DEAD10C5/badge-2023-tri-poloski/images/20230513_213218.jpg

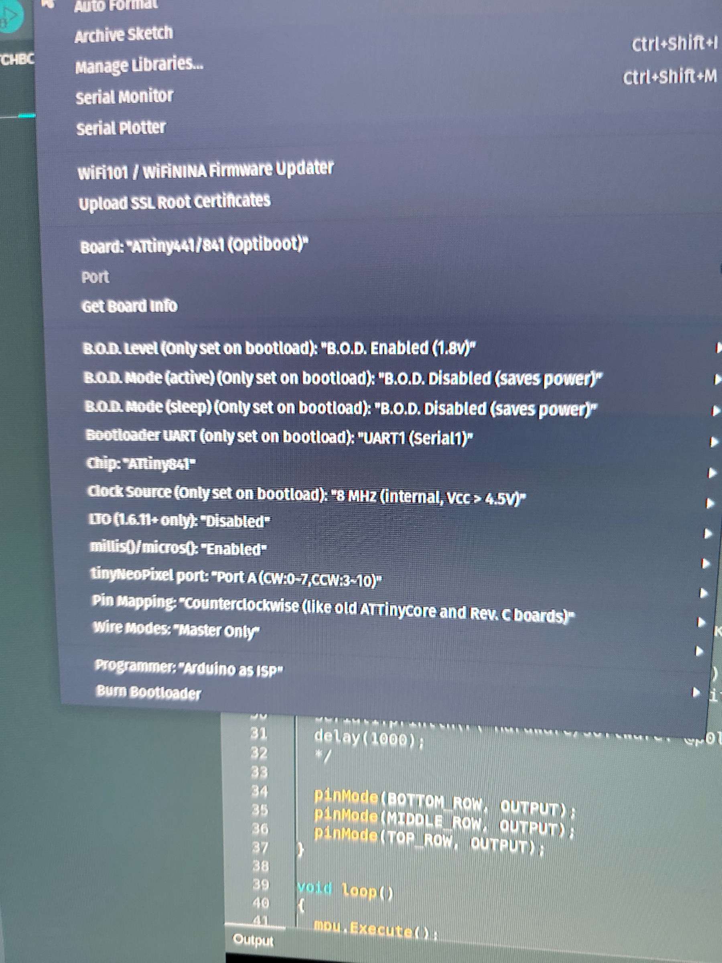
images/20230513_213218.jpg
