DEAD10C5/badge-2023-tri-poloski/images/adidas-back-3d-v2.png

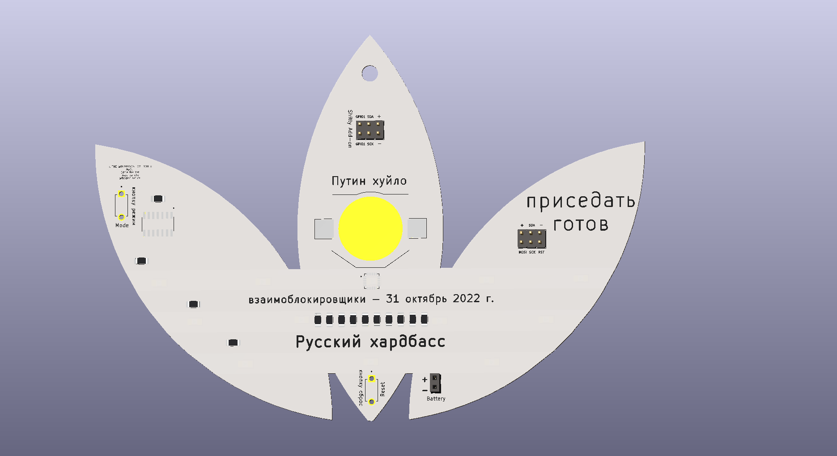
images/adidas-back-3d-v2.png
