DEAD10C5/badge-2023-tri-poloski/images/adidas-back-3d.png

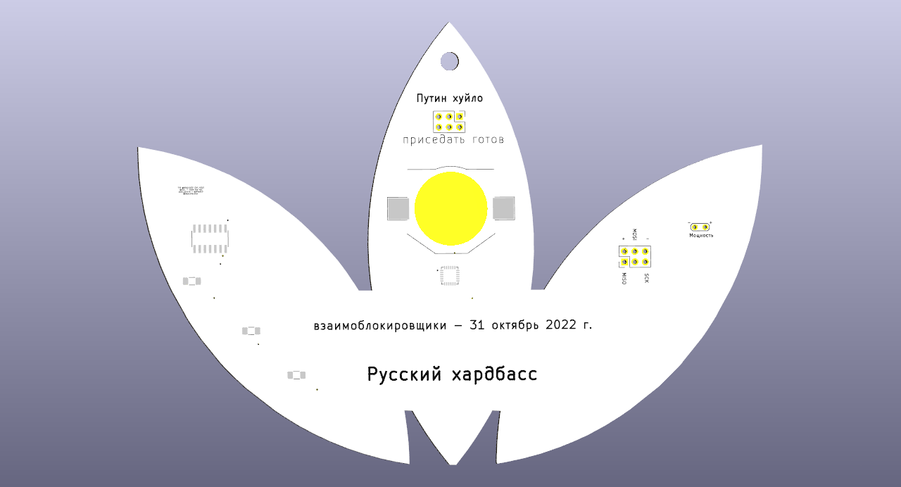
images/adidas-back-3d.png
