DEAD10C5/badge-2023-tri-poloski/images/adidas-brd2.png

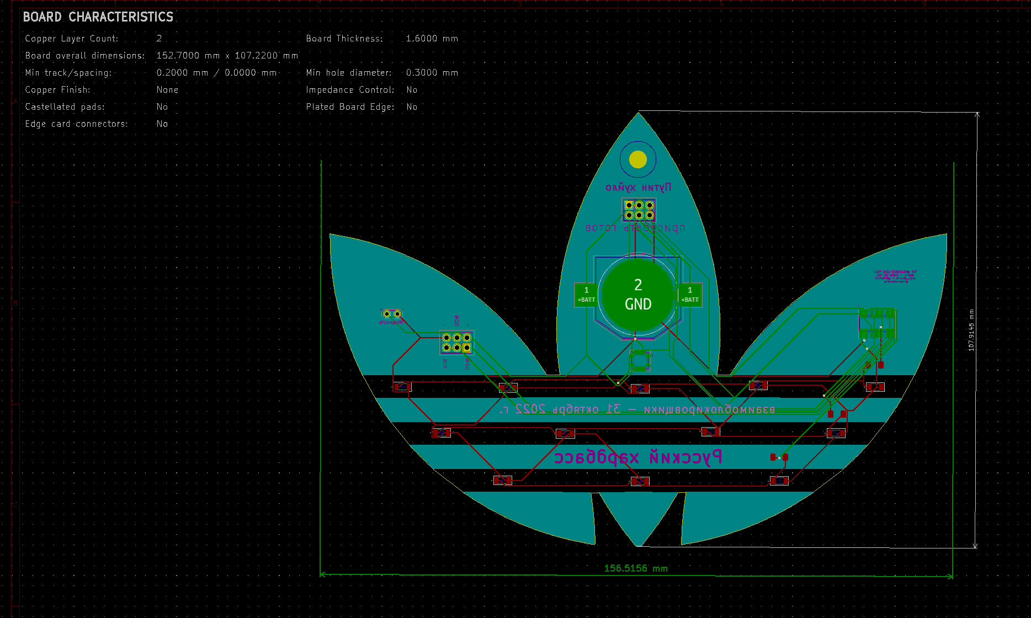
images/adidas-brd2.png
