DEAD10C5/badge-2023-tri-poloski/images/adidas-brd.png

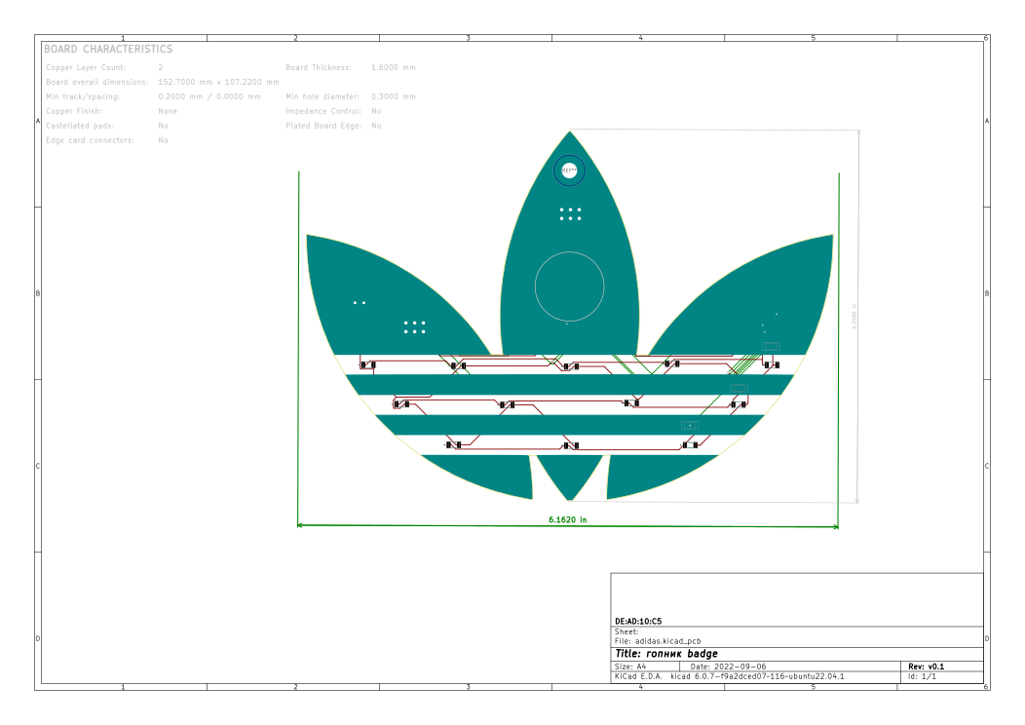
images/adidas-brd.png
