DEAD10C5/badge-2023-tri-poloski/images/adidas-front-3d.png

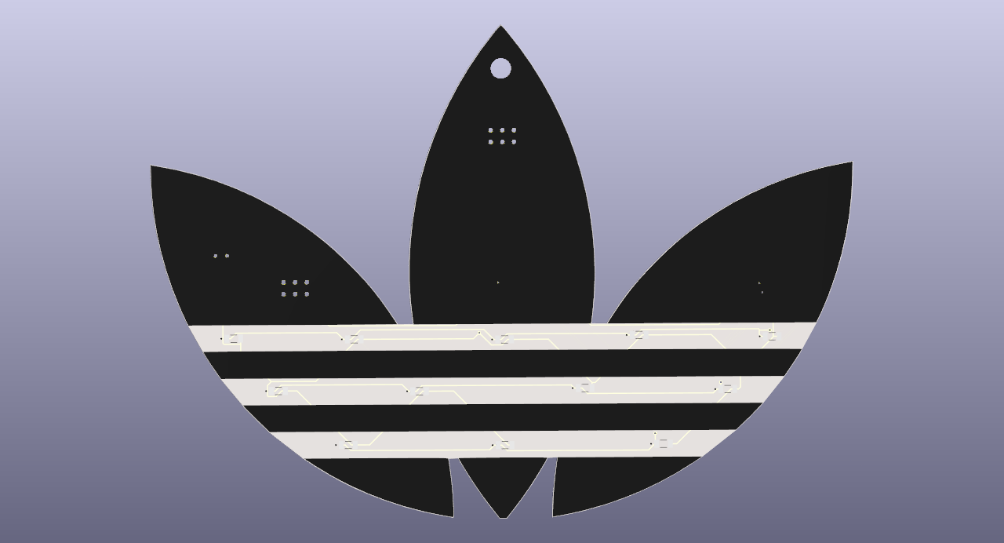
images/adidas-front-3d.png
