DEAD10C5/badge-2023-tri-poloski/images/almost_final2.png

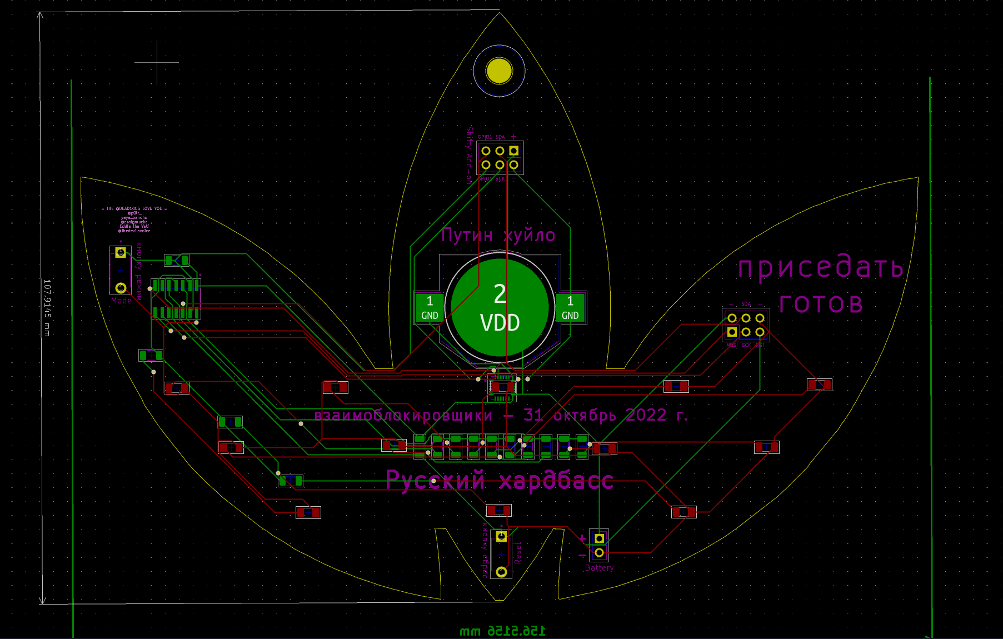
images/almost_final2.png
