DEAD10C5/badge-2023-tri-poloski/images/asdfasdf.png

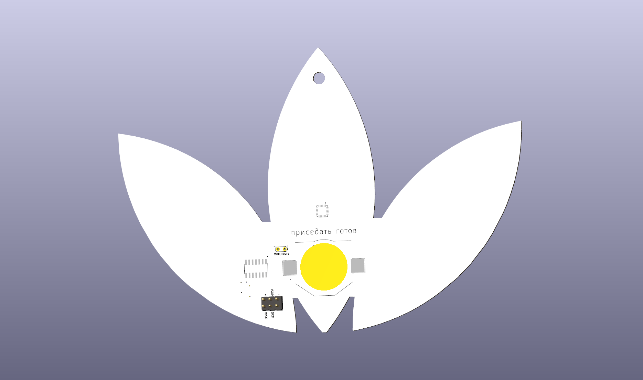
images/asdfasdf.png
