DEAD10C5/badge-2023-tri-poloski/images/ATtiny85-RGB.webp

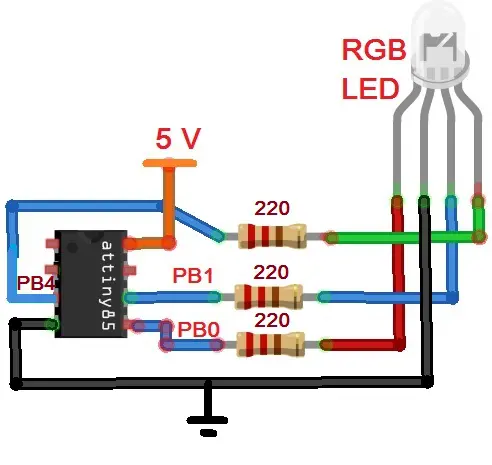
images/ATtiny85-RGB.webp
