DEAD10C5/badge-2023-tri-poloski/images/back1.jpg

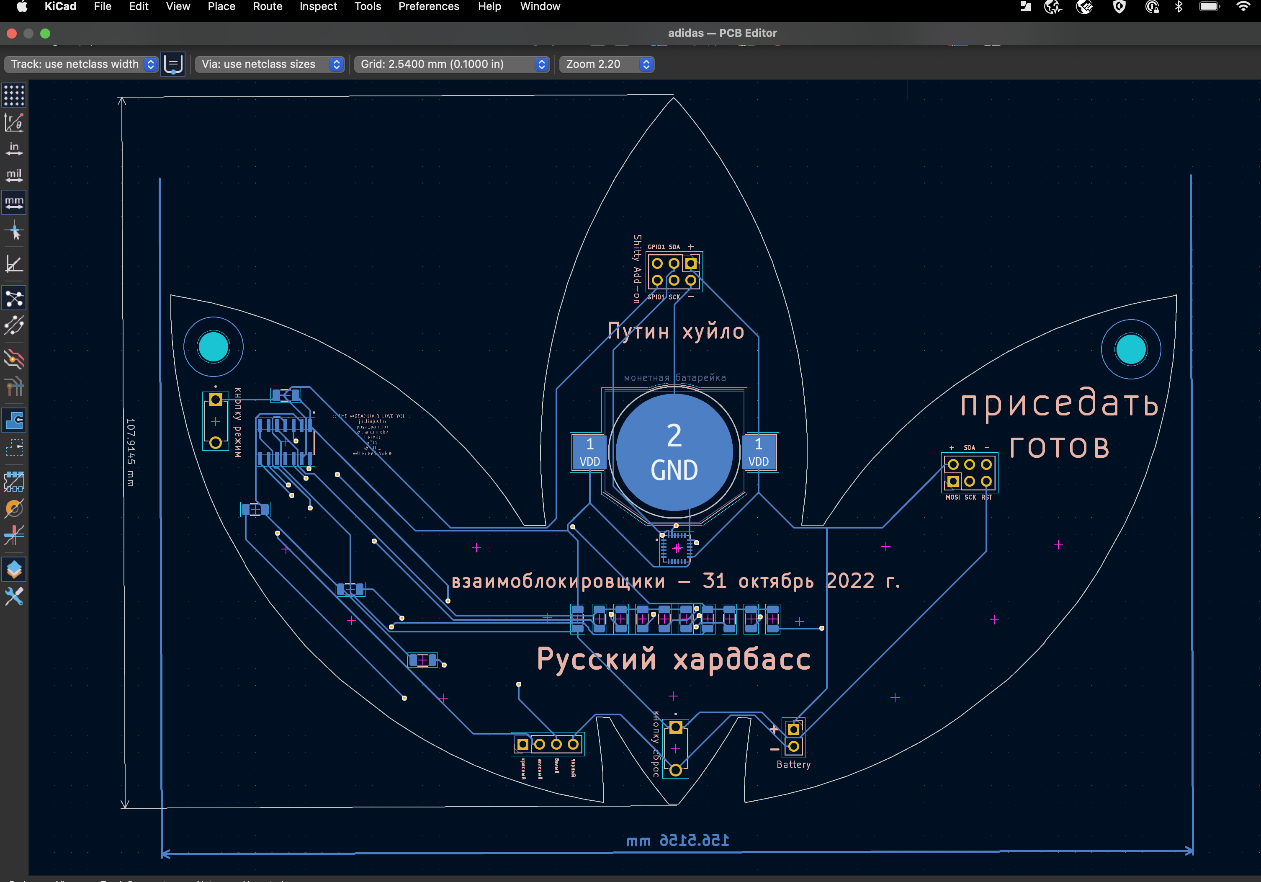
images/back1.jpg
