DEAD10C5/badge-2023-tri-poloski/images/dress.jpg

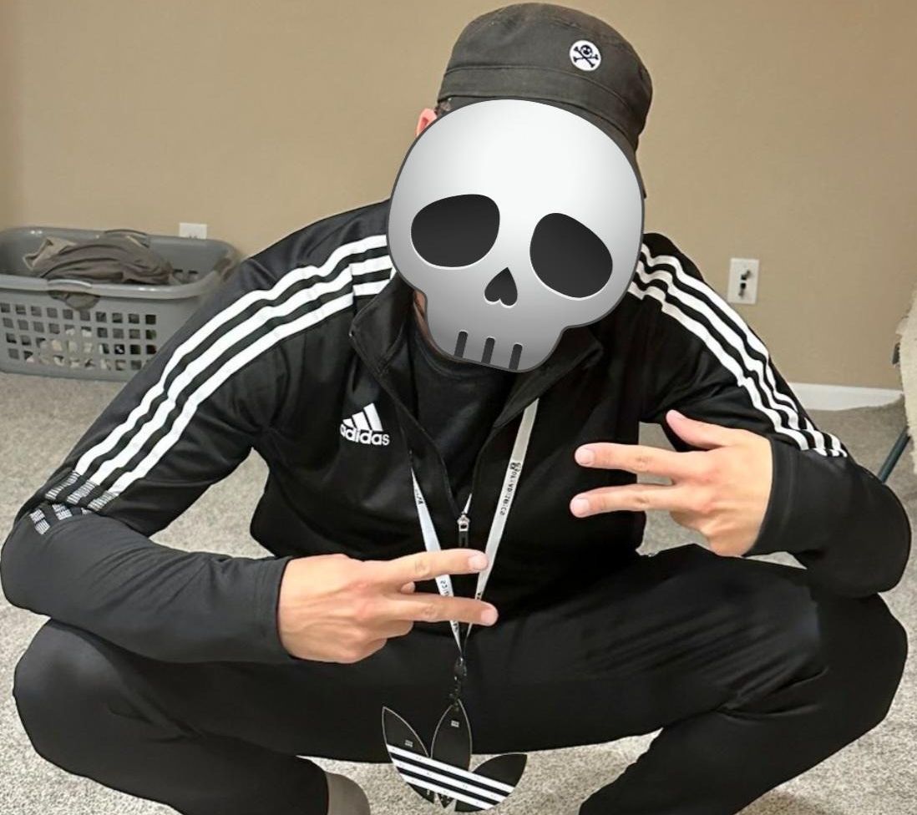
images/dress.jpg
