DEAD10C5/badge-2023-tri-poloski/images/final.png

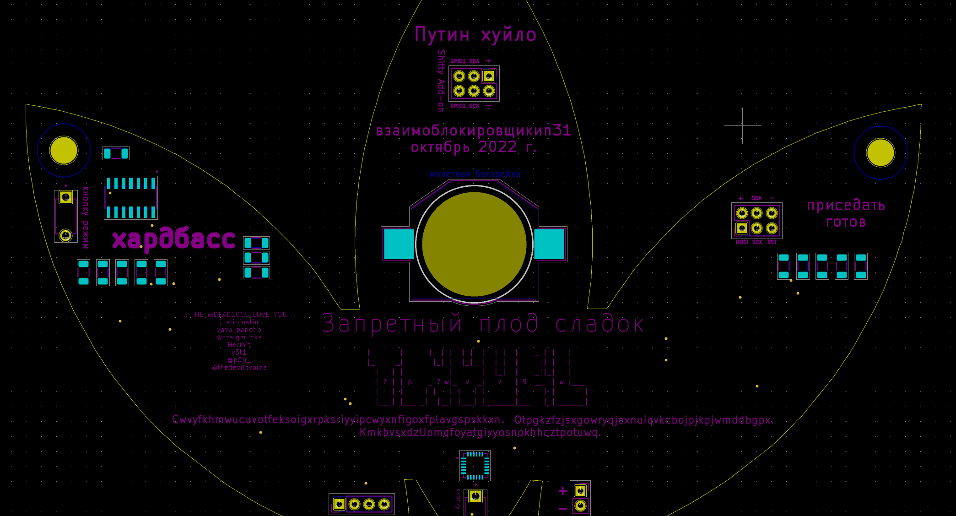
images/final.png
