DEAD10C5/badge-2023-tri-poloski/images/receipt1.png

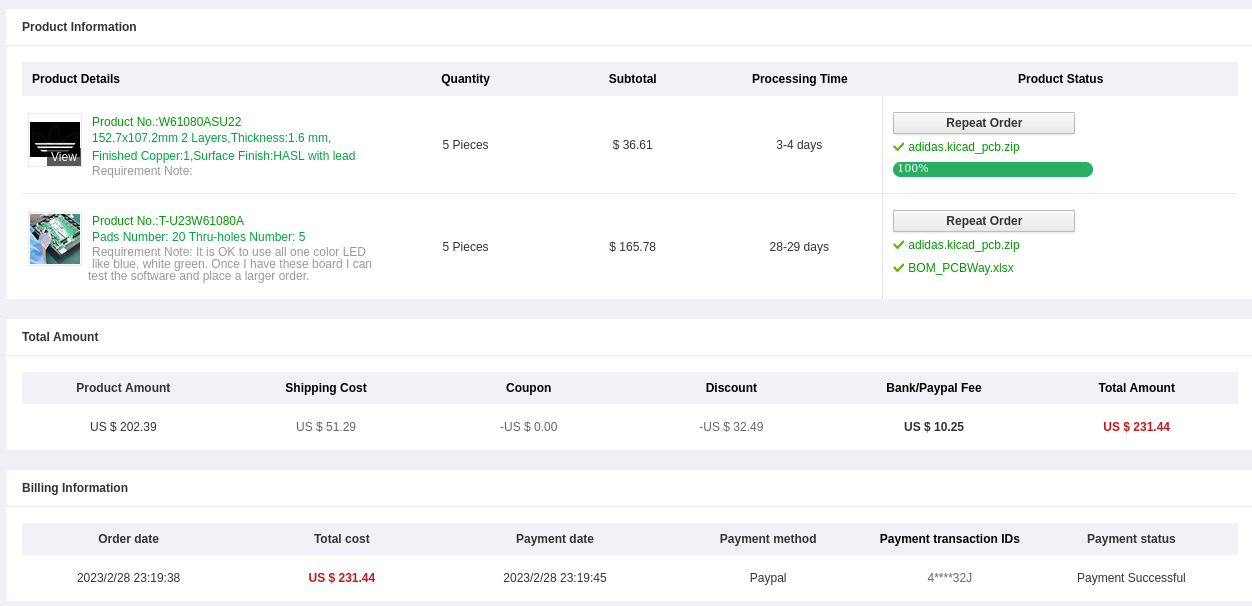
images/receipt1.png
