DEAD10C5/badge-2023-tri-poloski/images/Screenshot from 2022-09-07 18-56-25.png

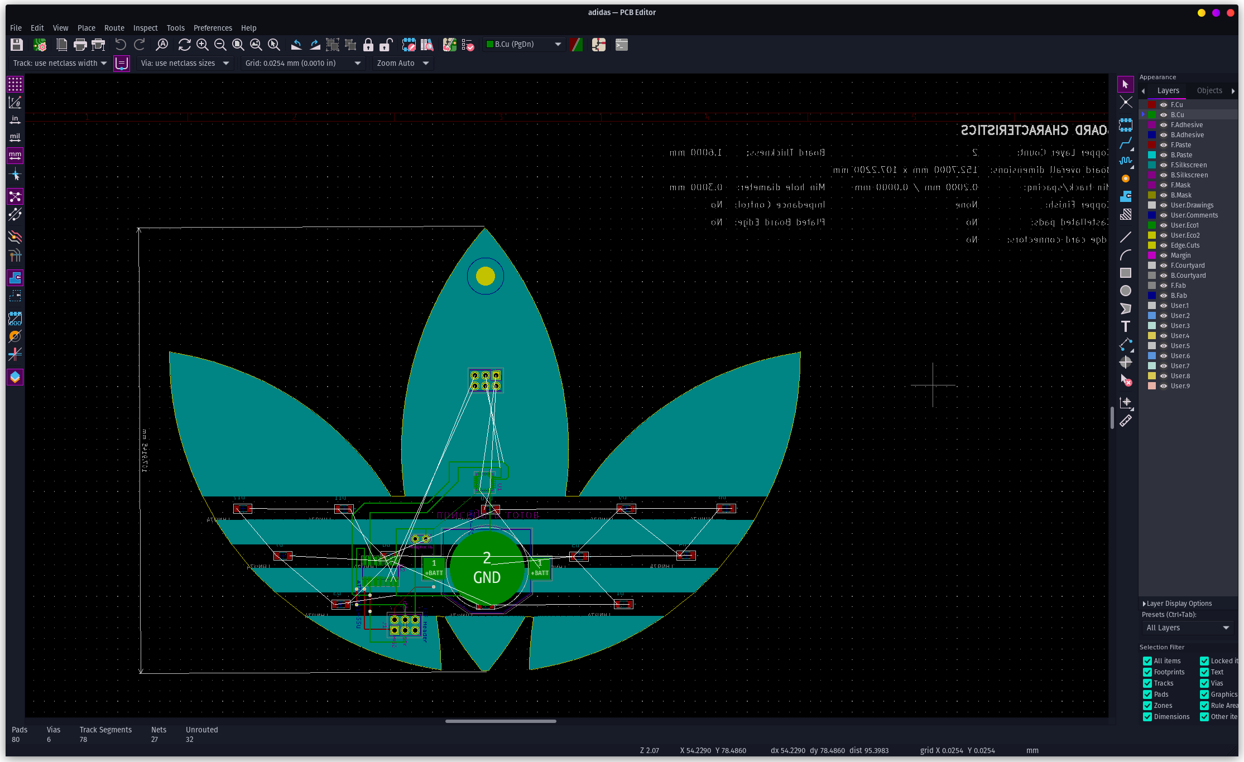
images/Screenshot from 2022-09-07 18-56-25.png
