DEAD10C5/badge-2023-tri-poloski/images/signal-2022-10-12-18-00-54-542.jpg

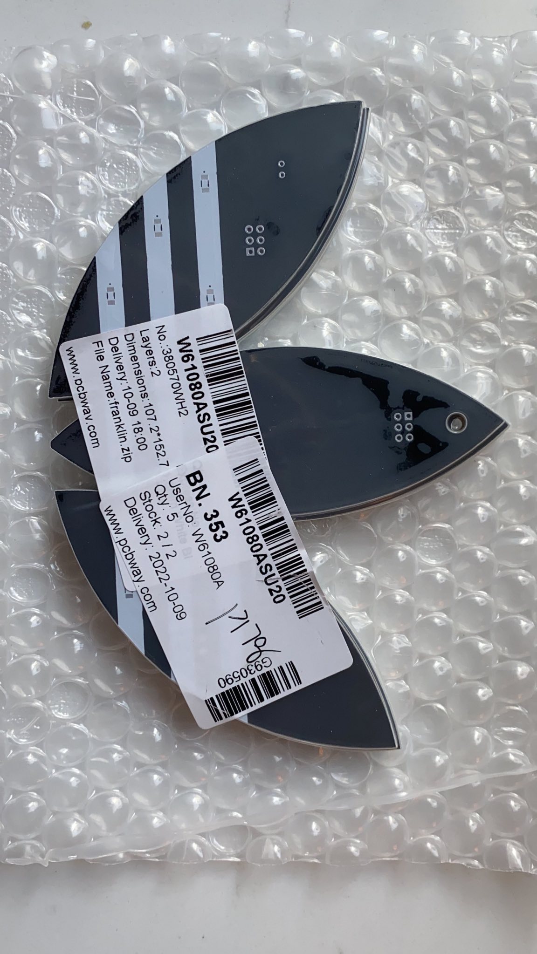
images/signal-2022-10-12-18-00-54-542.jpg
