DEAD10C5/badge-2023-tri-poloski/images/T-U29W61080A-01.png

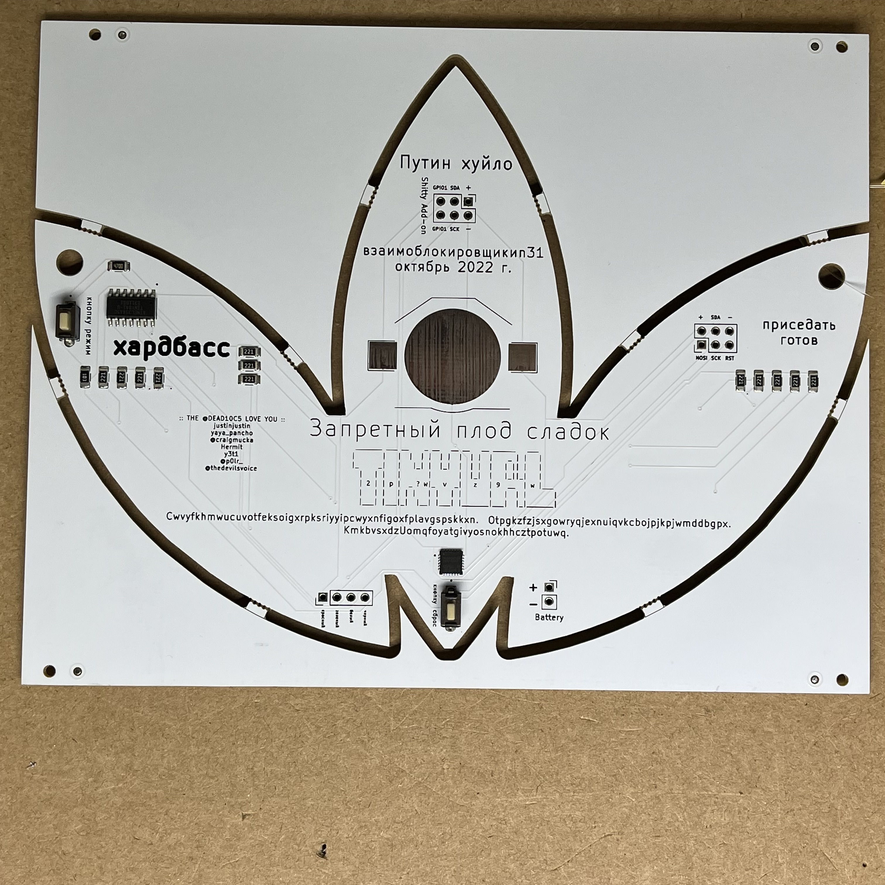
images/T-U29W61080A-01.png
