DEAD10C5/badge-2023-tri-poloski/puzzle/apple.png

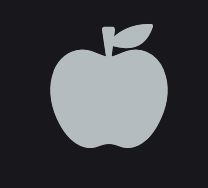
puzzle/apple.png
