DEAD10C5/badge-2023-tri-poloski/puzzle/melon.png

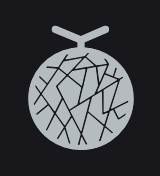
puzzle/melon.png
