DEAD10C5/badge-2023-tri-poloski/v3/docs/images/T-U23W61080A/3.jpg

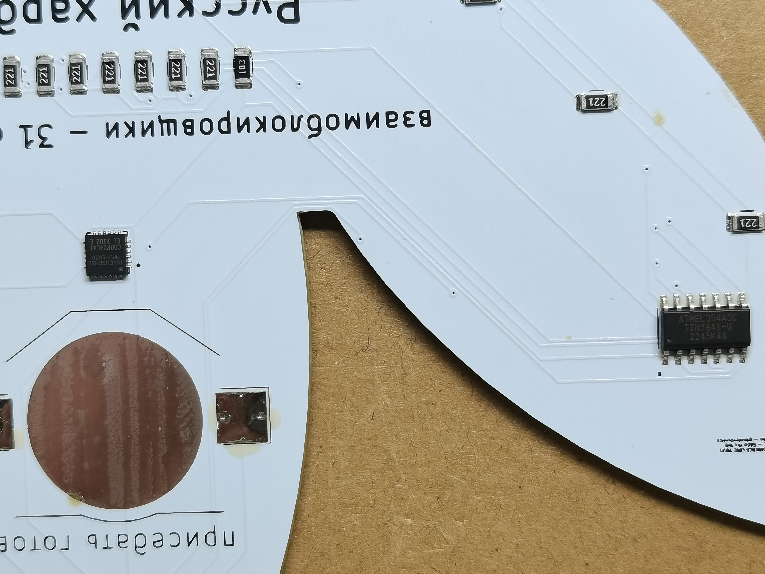
v3/docs/images/T-U23W61080A/3.jpg
