DEAD10C5/badge-2023-tri-poloski/v3/docs/images/T-U23W61080A/BACK-MPU6050.png

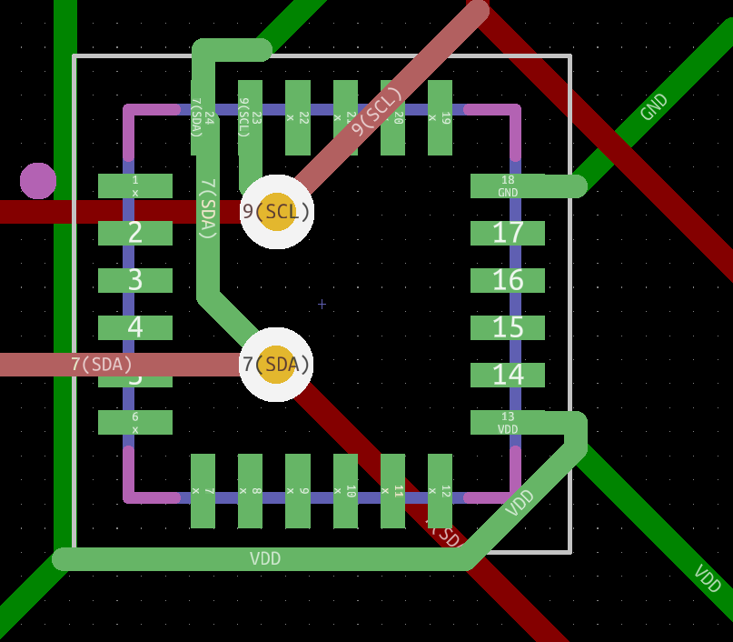
v3/docs/images/T-U23W61080A/BACK-MPU6050.png
