DEAD10C5/badge-2023-tri-poloski/images/bom-update.png

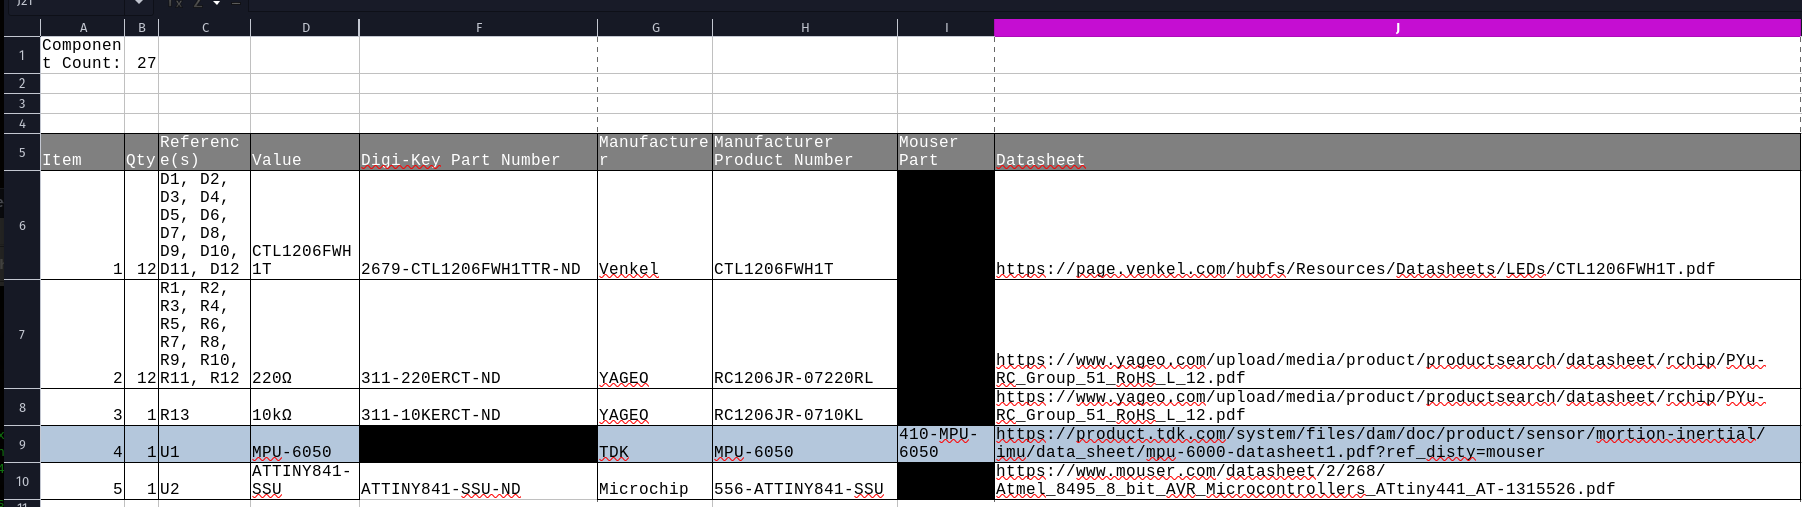
images/bom-update.png
